chuanyinn/digitizer-1/hw/sim/Digitizer_AFE.asc

C1: cap; 1µ
C2: cap; 100p
C3: cap; 50p
R1: res; 50
R2: res; 250
R3: res; 250
R4: res; 1000
R5: res; 1000
R6: res; 125
R7: res; 50
U1: opamp2; AD8014
V1: voltage; EXP(0 0 0 0 0 0); AC 0.1
V2: voltage; 3
V3: voltage; 5
V4: voltage; 0
Named nets: 0, Vin, Vout
.include AD8014.cir
*.tran -1ns 1000ns
.ac dec 100 100 10E+9
