chuanyinn/digitizer-1/fw/src/add10.vhdl

library ieee;
use ieee.std_logic_1164.all;

library machxo2;
use machxo2.components.all;

entity ADD10 is
    port(I_CLK: in  std_logic;
         I_L:   in  std_logic_vector(9 downto 0);
         I_M:   in  std_logic_vector(9 downto 0);
         O_N:   out std_logic_vector(9 downto 0);
         O_C:   out std_logic);
end ADD10;

architecture STRUCTURAL of ADD10 is
    component FD1S3AX is
        generic(GSR: string);
        port(CK: in  std_logic;
             D:  in  std_logic;
             Q:  out std_logic);
    end component;

    component ADD2 is
        port(I_L0: in  std_logic;
             I_L1: in  std_logic;
             I_M0: in  std_logic;
             I_M1: in  std_logic;
             O_N0: out std_logic;
             O_N1: out std_logic;
             O_C:  out std_logic);
    end component;

    signal S_CLK: std_logic;
    signal S_L:   std_logic_vector(9 downto 0);
    signal S_M:   std_logic_vector(9 downto 0);
    signal S_N:   std_logic_vector(9 downto 0);
    signal S_C:   std_logic;

    signal S_ADD2_1_N0: std_logic;
    signal S_ADD2_1_N1: std_logic;
    signal S_ADD2_1_C:  std_logic;

    signal S_ADD2_2_N0: std_logic;
    signal S_ADD2_2_N1: std_logic;
    signal S_ADD2_2_C:  std_logic;

    signal S_ADD2_3_N0: std_logic;
    signal S_ADD2_3_N1: std_logic;
    signal S_ADD2_3_C:  std_logic;

    signal S_ADD2_4_N0: std_logic;
    signal S_ADD2_4_N1: std_logic;
    signal S_ADD2_4_C:  std_logic;

    signal S_ADD2_5_N0: std_logic;
    signal S_ADD2_5_N1: std_logic;
    signal S_ADD2_5_C:  std_logic;

    signal S_DTFF1_Q:  std_logic;
    signal S_DTFF2_Q:  std_logic;
    signal S_DTFF3_Q:  std_logic;
    signal S_DTFF4_Q:  std_logic;
    signal S_DTFF5_Q:  std_logic;
    signal S_DTFF6_Q:  std_logic;
    signal S_DTFF7_Q:  std_logic;
    signal S_DTFF8_Q:  std_logic;
    signal S_DTFF9_Q:  std_logic;
    signal S_DTFF10_Q: std_logic;
    signal S_DTFF11_Q: std_logic;
    signal S_DTFF12_Q: std_logic;
    signal S_DTFF13_Q: std_logic;
    signal S_DTFF14_Q: std_logic;
    signal S_DTFF15_Q: std_logic;

    signal S_ADD2_6_N0: std_logic;
    signal S_ADD2_6_N1: std_logic;
    signal S_ADD2_6_C:  std_logic;

    signal S_ADD2_7_N0: std_logic;
    signal S_ADD2_7_N1: std_logic;
    signal S_ADD2_7_C:  std_logic;

    signal S_ADD2_8_N0: std_logic;
    signal S_ADD2_8_N1: std_logic;
    signal S_ADD2_8_C:  std_logic;

    signal S_ADD2_9_N0: std_logic;
    signal S_ADD2_9_N1: std_logic;
    signal S_ADD2_9_C:  std_logic;

    signal S_OR1: std_logic;

    signal S_DTFF16_Q: std_logic;
    signal S_DTFF17_Q: std_logic;
    signal S_DTFF18_Q: std_logic;
    signal S_DTFF19_Q: std_logic;
    signal S_DTFF20_Q: std_logic;
    signal S_DTFF21_Q: std_logic;
    signal S_DTFF22_Q: std_logic;
    signal S_DTFF23_Q: std_logic;
    signal S_DTFF24_Q: std_logic;
    signal S_DTFF25_Q: std_logic;
    signal S_DTFF26_Q: std_logic;
    signal S_DTFF27_Q: std_logic;
    signal S_DTFF28_Q: std_logic;
    signal S_DTFF29_Q: std_logic;

    signal S_ADD2_10_N0: std_logic;
    signal S_ADD2_10_N1: std_logic;
    signal S_ADD2_10_C:  std_logic;

    signal S_ADD2_11_N0: std_logic;
    signal S_ADD2_11_N1: std_logic;
    signal S_ADD2_11_C:  std_logic;

    signal S_ADD2_12_N0: std_logic;
    signal S_ADD2_12_N1: std_logic;
    signal S_ADD2_12_C:  std_logic;

    signal S_OR2: std_logic;

    signal S_DTFF30_Q: std_logic;
    signal S_DTFF31_Q: std_logic;
    signal S_DTFF32_Q: std_logic;
    signal S_DTFF33_Q: std_logic;
    signal S_DTFF34_Q: std_logic;
    signal S_DTFF35_Q: std_logic;
    signal S_DTFF36_Q: std_logic;
    signal S_DTFF37_Q: std_logic;
    signal S_DTFF38_Q: std_logic;
    signal S_DTFF39_Q: std_logic;
    signal S_DTFF40_Q: std_logic;
    signal S_DTFF41_Q: std_logic;
    signal S_DTFF42_Q: std_logic;

    signal S_ADD2_13_N0: std_logic;
    signal S_ADD2_13_N1: std_logic;
    signal S_ADD2_13_C:  std_logic;

    signal S_ADD2_14_N0: std_logic;
    signal S_ADD2_14_N1: std_logic;
    signal S_ADD2_14_C:  std_logic;

    signal S_OR3: std_logic;

    signal S_DTFF43_Q: std_logic;
    signal S_DTFF44_Q: std_logic;
    signal S_DTFF45_Q: std_logic;
    signal S_DTFF46_Q: std_logic;
    signal S_DTFF47_Q: std_logic;
    signal S_DTFF48_Q: std_logic;
    signal S_DTFF49_Q: std_logic;
    signal S_DTFF50_Q: std_logic;
    signal S_DTFF51_Q: std_logic;
    signal S_DTFF52_Q: std_logic;
    signal S_DTFF53_Q: std_logic;
    signal S_DTFF54_Q: std_logic;

    signal S_ADD2_15_N0: std_logic;
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
                             Q  => S_N(9));
    --
    DTFF65: FD1S3AX generic map(GSR => "ENABLED")
                    port map(CK => S_CLK,
                             D  => S_OR4,
                             Q  => S_C);
    --
    O_N <= S_N;
    O_C <= S_C;
end STRUCTURAL;
